Emu-gators/floppy-overdrive/pcb_tests/external_header/external_header.v

/*
 *  
 *  Modified by Thomas Le, Spring 2023
 *  Copyright(C) 2018 Gerald Coe, Devantech Ltd <gerry@devantech.co.uk>
 * 
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
 */


// Pulse the external breakout pins at 1 kHz
/* module */
module top (
    input clk,
    output bus0, bus1, bus2, bus3, bus4, bus5, bus6, bus7, bus8, bus9,
    output bus10, bus11, bus12, bus13, bus14, bus15, bus16, bus17, bus18, bus19,
    output bus20, bus21, bus22, bus23, bus24, bus25, bus26, bus27, bus28, bus29,
    output bus30, bus31, bus32, bus33, bus34, bus35, bus36
    );

    /* I/O */
    wire [36:0] bus_out;

    localparam TIMER_HALF = 50000;
    localparam TIMER_FULL = TIMER_HALF*2;

    /* Counter register */
    reg [31:0] counter = 32'b0;

    wire pll_clk;
    wire locked;
    pll U_PLL(.clock_in(clk), .global_clock(pll_clk), .locked(locked));

    /* LED drivers - counter is inverted for display because leds are active low */
    always @* begin
        if(counter < TIMER_HALF) begin
            bus_out = {37{1'b0}};
        end
        else begin
            bus_out = {37{1'b1}};
        end
    end


    /* Count up on every edge of the incoming 50MHz PLL clk */
    always @ (posedge pll_clk) begin
        counter <= counter + 1;

        if(counter > TIMER_FULL) begin
            counter <= 32'b0;
        end
    end

    assign bus0 = bus_out[0];
    assign bus1 = bus_out[1];
    assign bus2 = bus_out[2];
    assign bus3 = bus_out[3];
    assign bus4 = bus_out[4];
    assign bus5 = bus_out[5];
    assign bus6 = bus_out[6];
    assign bus7 = bus_out[7];
    assign bus8 = bus_out[8];
    assign bus9 = bus_out[9];
    assign bus10 = bus_out[10];
    assign bus11 = bus_out[11];
    assign bus12 = bus_out[12];
    assign bus13 = bus_out[13];
    assign bus14 = bus_out[14];
    assign bus15 = bus_out[15];
    assign bus16 = bus_out[16];
    assign bus17 = bus_out[17];
    assign bus18 = bus_out[18];
    assign bus19 = bus_out[19];
    assign bus20 = bus_out[20];
    assign bus21 = bus_out[21];
    assign bus22 = bus_out[22];
    assign bus23 = bus_out[23];
    assign bus24 = bus_out[24];
    assign bus25 = bus_out[25];
    assign bus26 = bus_out[26];
    assign bus27 = bus_out[27];
    assign bus28 = bus_out[28];
    assign bus29 = bus_out[29];
    assign bus30 = bus_out[30];
    assign bus31 = bus_out[31];
    assign bus32 = bus_out[32];
    assign bus33 = bus_out[33];
    assign bus34 = bus_out[34];
    assign bus35 = bus_out[35];
    assign bus36 = bus_out[36];

endmodule
